18Markus1984/Volume-Knob/images/PXL_20210518_220217946.jpg

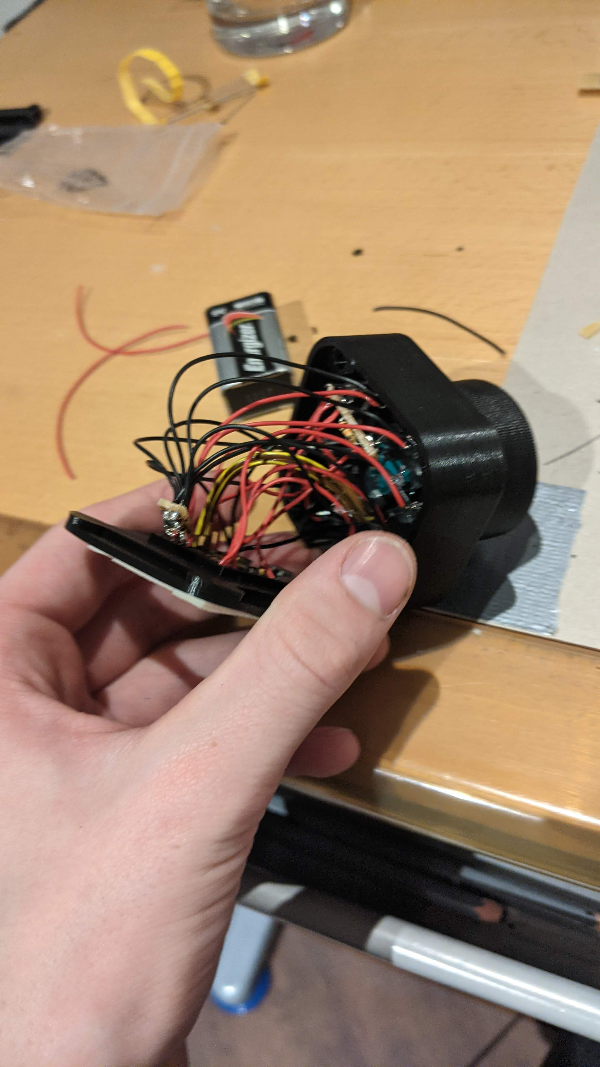
images/PXL_20210518_220217946.jpg
