18Markus1984/Volume-Knob/ProMicroKiCad-master/arduino-pro-micro-1.snapshot.1/PROMICRO 2.JPG

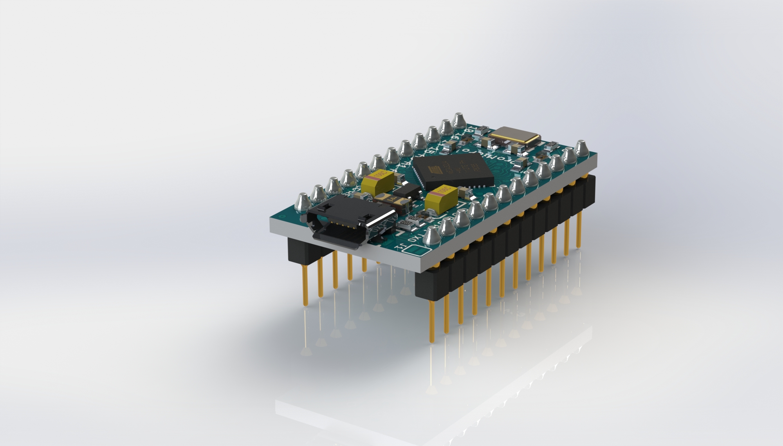
ProMicroKiCad-master/arduino-pro-micro-1.snapshot.1/PROMICRO 2.JPG
