18Markus1984/Volume-Knob/ProMicroKiCad-master/VolumeKnob/BackUpBevorKiKit/BoardPanalized.png

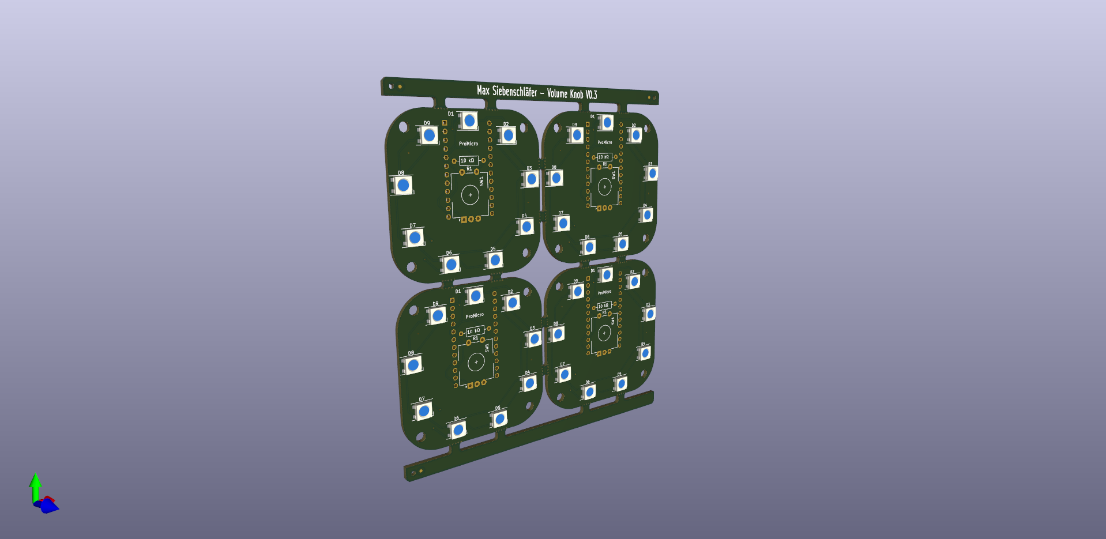
ProMicroKiCad-master/VolumeKnob/BackUpBevorKiKit/BoardPanalized.png
