18Markus1984/Volume-Knob/ProMicroKiCad-master/VolumeKnob/Objekts/RotaryEncoderV2.stp

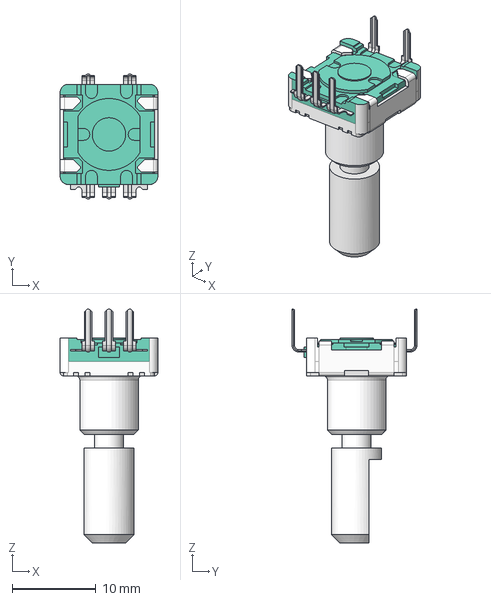
[picture p29: CAD file, 2022-02-25]
ProMicroKiCad-master/VolumeKnob/Objekts/RotaryEncoderV2.stp
11.7 x 14.9 x 28.0 mm
