18Markus1984/Volume-Knob/ProMicroKiCad-master/VolumeKnob/3DObjekt/PCB-Holder.stl

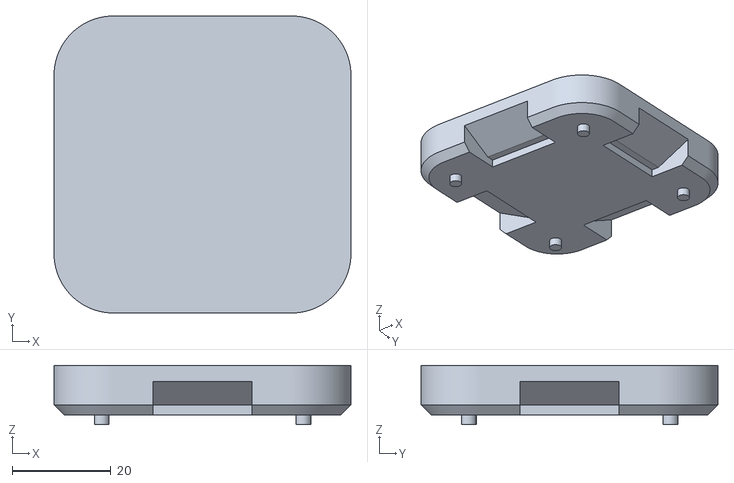
[picture p30: CAD file, 2022-03-25]
ProMicroKiCad-master/VolumeKnob/3DObjekt/PCB-Holder.stl
60.0 x 60.0 x 12.0
