18Markus1984/Volume-Knob/ProMicroKiCad-master/VolumeKnob/3DObjekt/TransfuserDurchgehend.stl

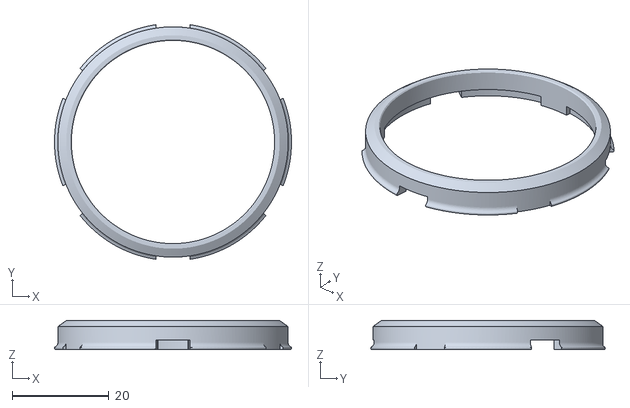
[picture p31: CAD file, 2022-02-25]
ProMicroKiCad-master/VolumeKnob/3DObjekt/TransfuserDurchgehend.stl
49.0 x 48.5 x 6.00
