18Markus1984/Volume-Knob/ProMicroKiCad-master/VolumeKnob/3DObjekt/Bodenplatte(USB-C).stl

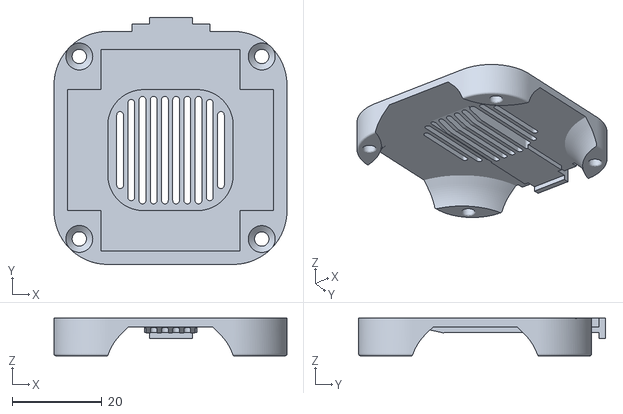
[picture p32: CAD file, 2022-02-25]
ProMicroKiCad-master/VolumeKnob/3DObjekt/Bodenplatte(USB-C).stl
52.0 x 55.1 x 8.40
