18Markus1984/Volume-Knob/ProMicroKiCad-master/VolumeKnob/3DObjekt/Transfuser.stl

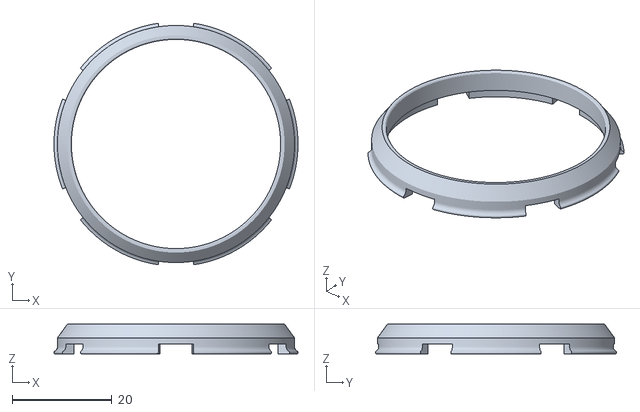
[picture p33: CAD file, 2022-02-25]
ProMicroKiCad-master/VolumeKnob/3DObjekt/Transfuser.stl
49.0 x 48.5 x 6.00
