18Markus1984/Volume-Knob/ProMicroKiCad-master/VolumeKnob/3DObjekt/Bodenplatte.stl

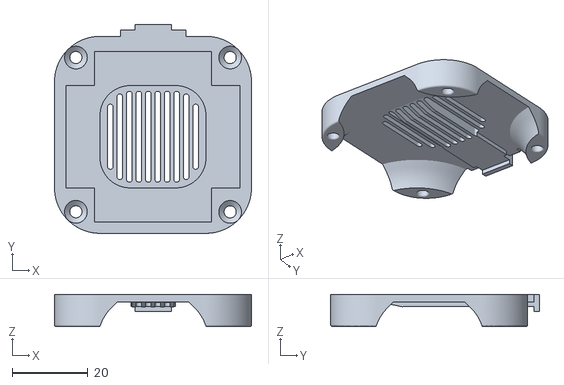
[picture p34: CAD file, 2022-02-25]
ProMicroKiCad-master/VolumeKnob/3DObjekt/Bodenplatte.stl
52.0 x 55.1 x 8.50
