18Markus1984/Volume-Knob/ProMicroKiCad-master/VolumeKnob/3DObjekt/Oberbau.stl

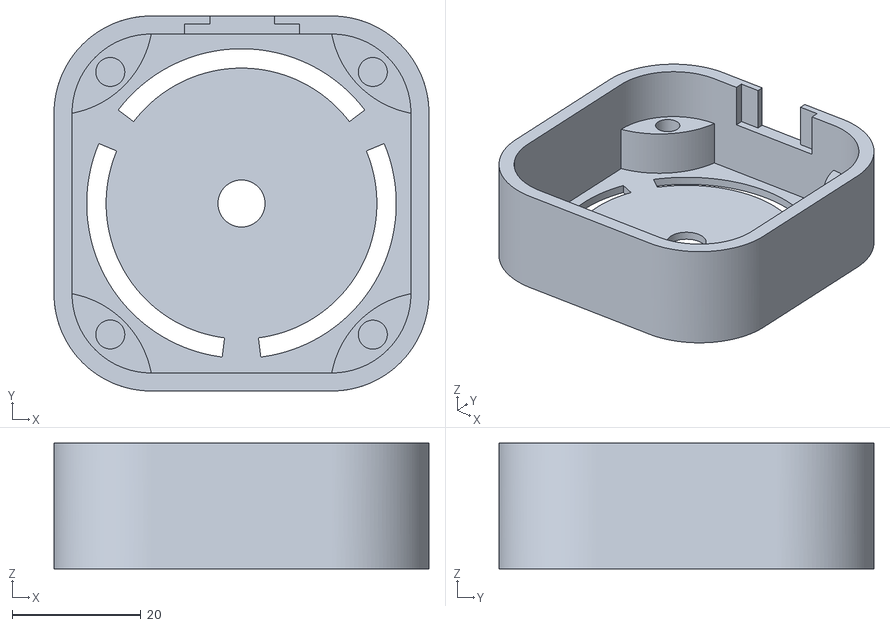
[picture p35: CAD file, 2022-02-25]
ProMicroKiCad-master/VolumeKnob/3DObjekt/Oberbau.stl
58.2 x 58.2 x 19.5
