18Markus1984/Volume-Knob/ProMicroKiCad-master/VolumeKnob/3DObjekt/Drehregler.stl

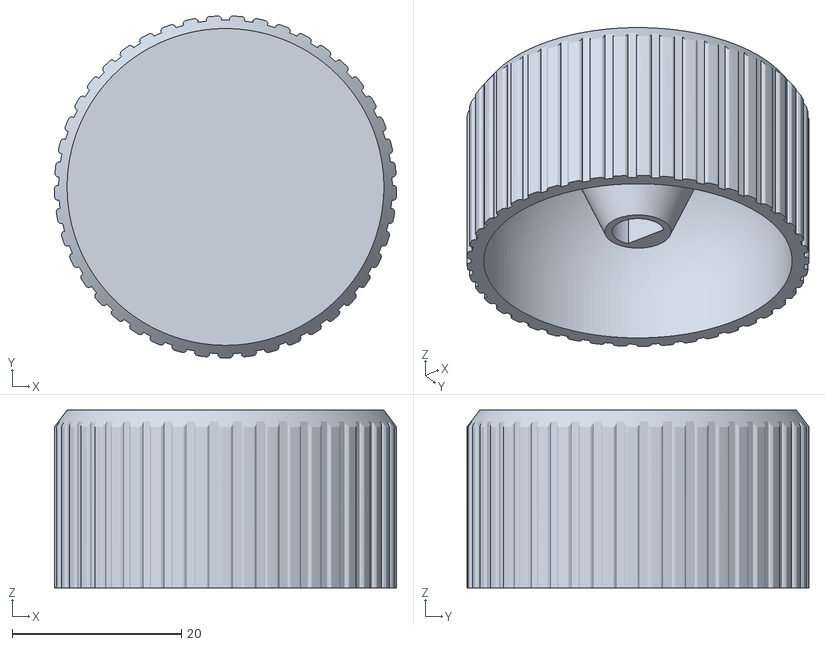
[picture p36: CAD file, 2022-02-25]
ProMicroKiCad-master/VolumeKnob/3DObjekt/Drehregler.stl
40.4 x 40.4 x 21.0
